madnordski/ZenithVCR/photos/20250118_151705.jpg

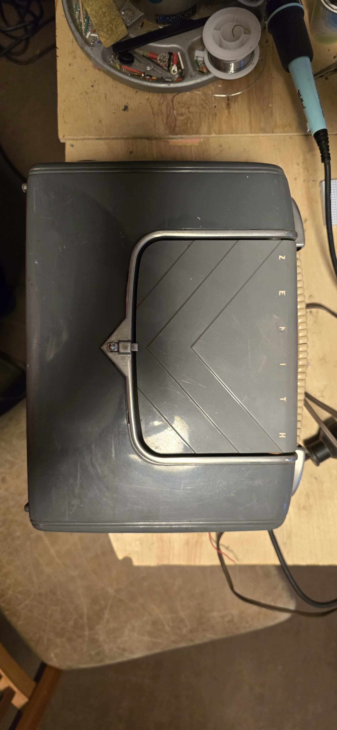
photos/20250118_151705.jpg
