madnordski/ZenithVCR/photos/20250121_075249.jpg

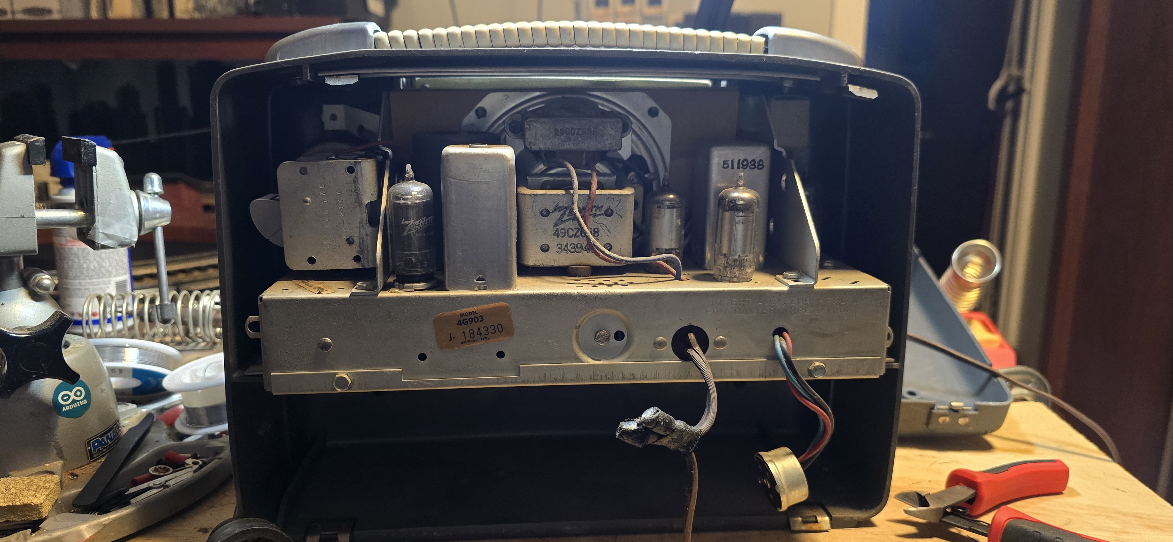
photos/20250121_075249.jpg
