madnordski/ZenithVCR/photos/20250125_090254.jpg

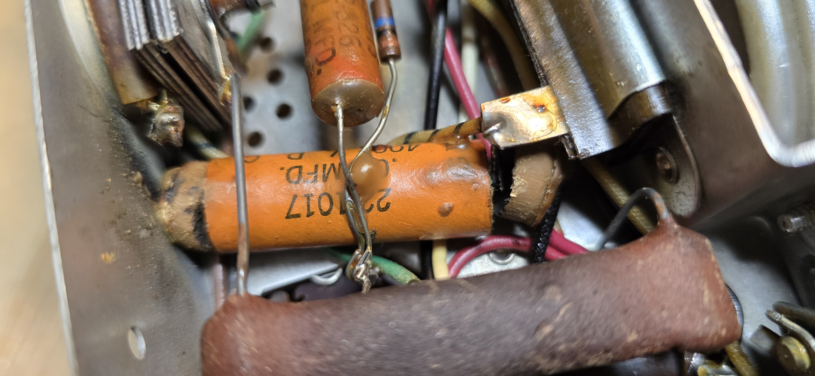
photos/20250125_090254.jpg
