madnordski/ZenithVCR/photos/20250125_091158.jpg

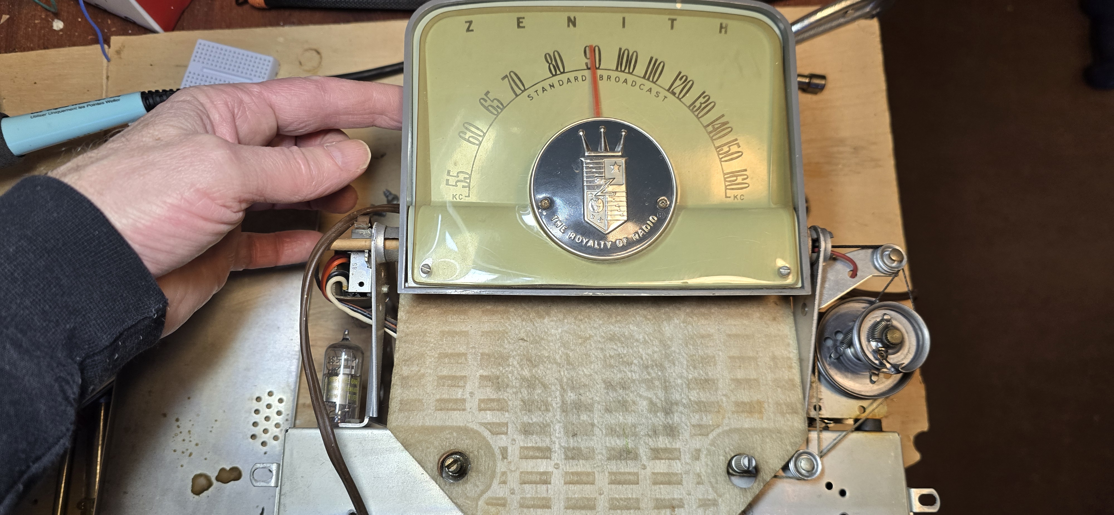
photos/20250125_091158.jpg
