madnordski/ZenithVCR/photos/20250211_211813.jpg

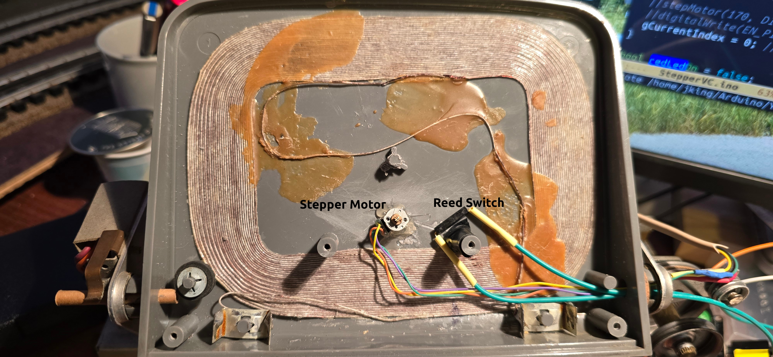
photos/20250211_211813.jpg
