madnordski/ZenithVCR/photos/20250215_073755.jpg

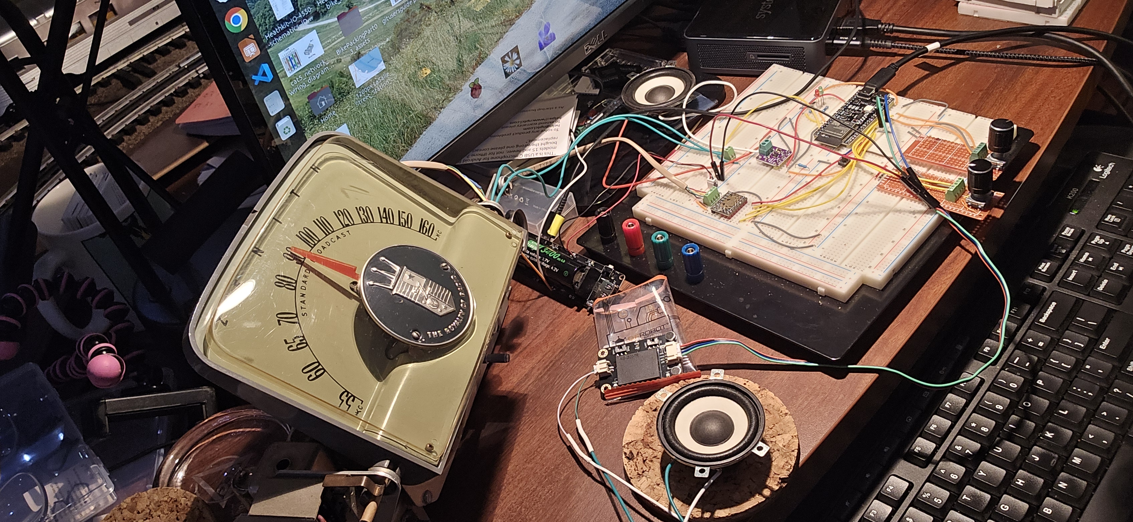
photos/20250215_073755.jpg
