madnordski/ZenithVCR/photos/20250216_142206.jpg

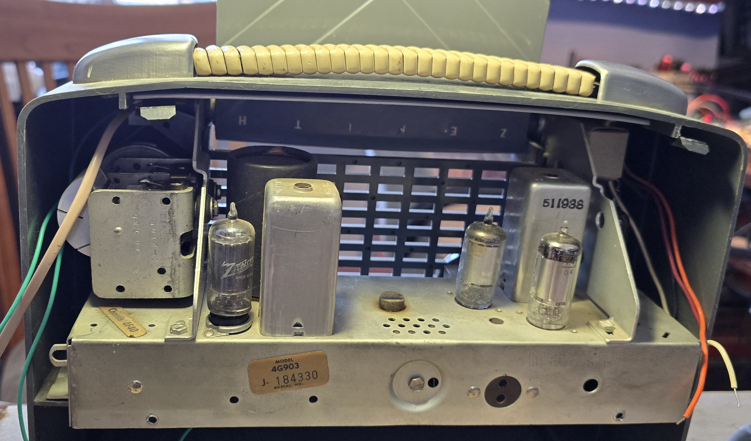
photos/20250216_142206.jpg
