madnordski/ZenithVCR/photos/20250220_070225.jpg

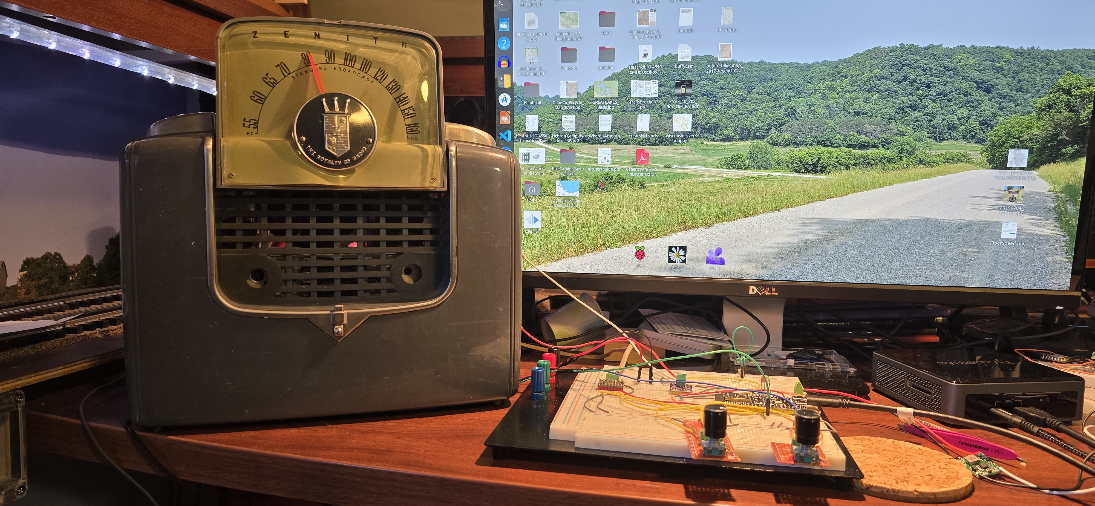
photos/20250220_070225.jpg
