madnordski/ZenithVCR/photos/20250226_121308.jpg

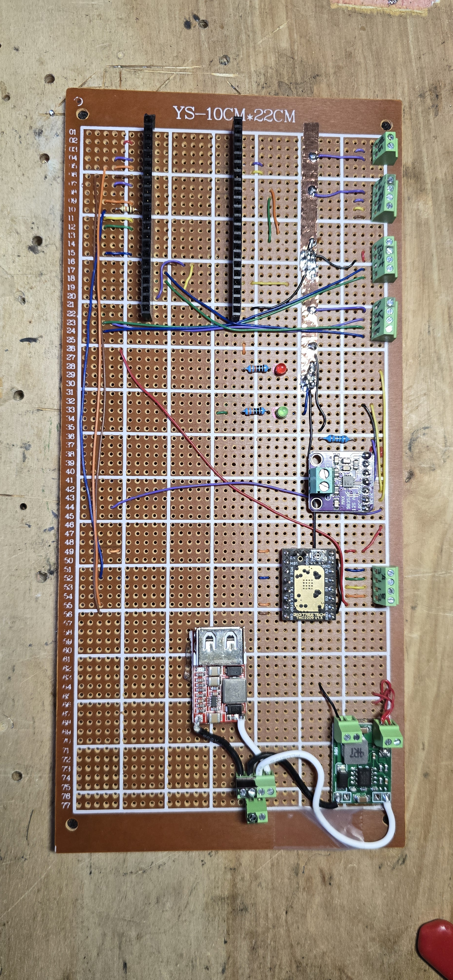
photos/20250226_121308.jpg
