madnordski/ZenithVCR/photos/20250226_122020.jpg

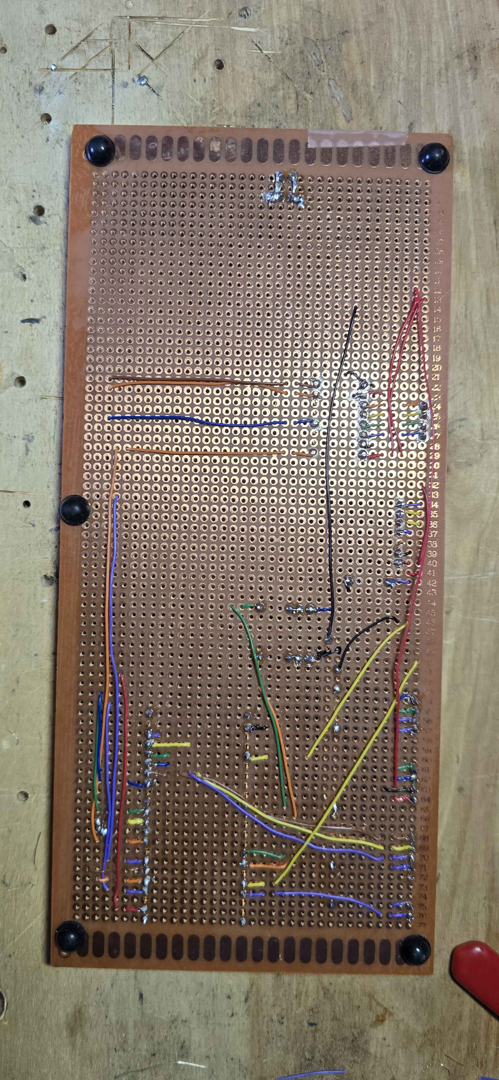
photos/20250226_122020.jpg
