madnordski/ZenithVCR/photos/20250226_133442.jpg

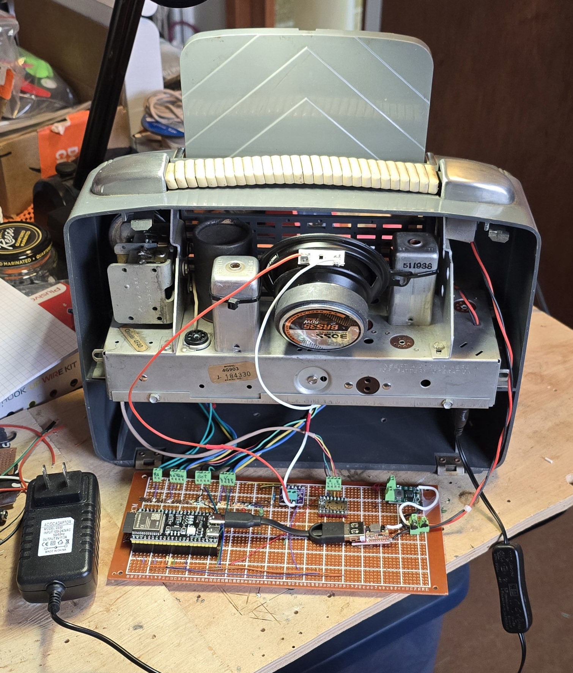
photos/20250226_133442.jpg
