madnordski/ZenithVCR/photos/20250226_150603.jpg

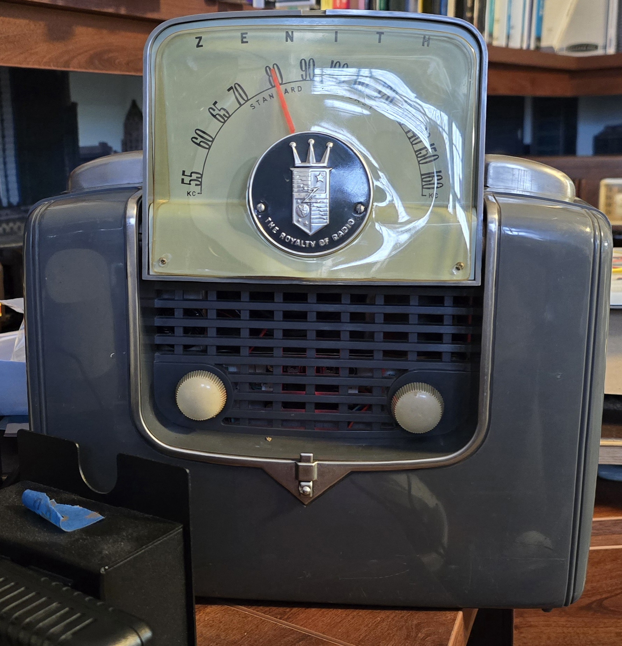
photos/20250226_150603.jpg
