madnordski/ZenithVCR/Parts/max98357a_front.jpg

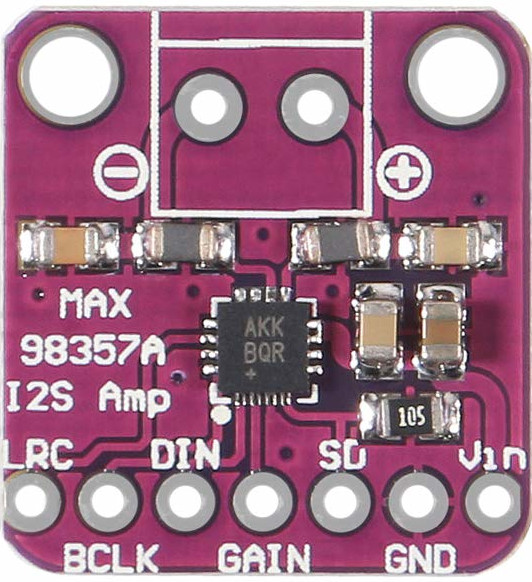
Parts/max98357a_front.jpg
